thetransistor/OpenWest2015/AddOnKit/Software/BMP Loader/img/1.bmp

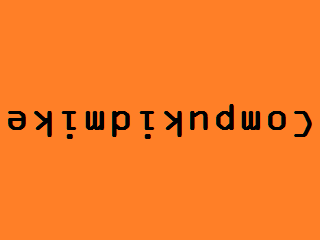
AddOnKit/Software/BMP Loader/img/1.bmp
