thetransistor/OpenWest2015/AddOnKit/Software/BMP Loader/img/default.bmp

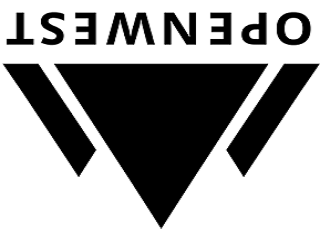
AddOnKit/Software/BMP Loader/img/default.bmp
