thetransistor/OpenWest2015/images/attiny85-board-location.jpg

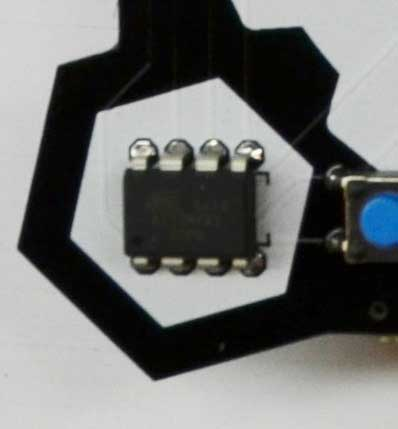
images/attiny85-board-location.jpg
