thetransistor/OpenWest2015/images/attiny85-zoom.jpg

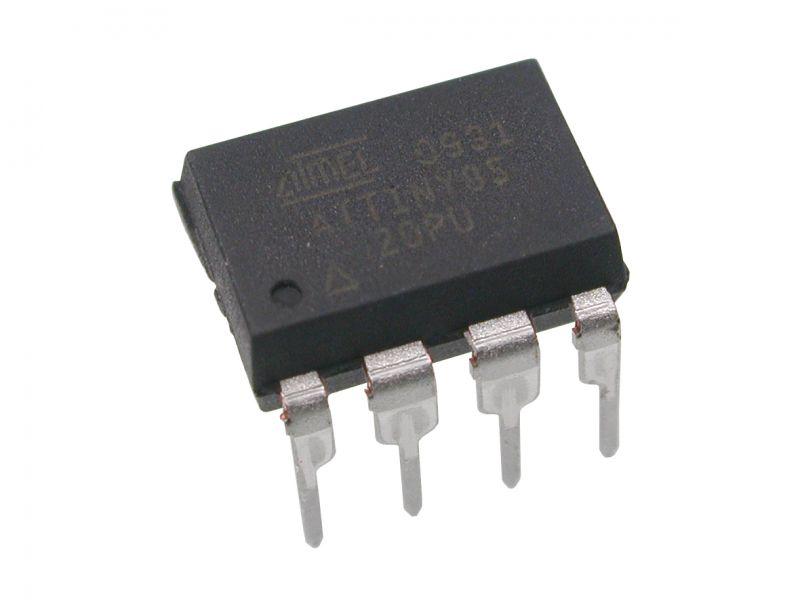
images/attiny85-zoom.jpg
