thetransistor/OpenWest2015/images/battery-holder.jpg

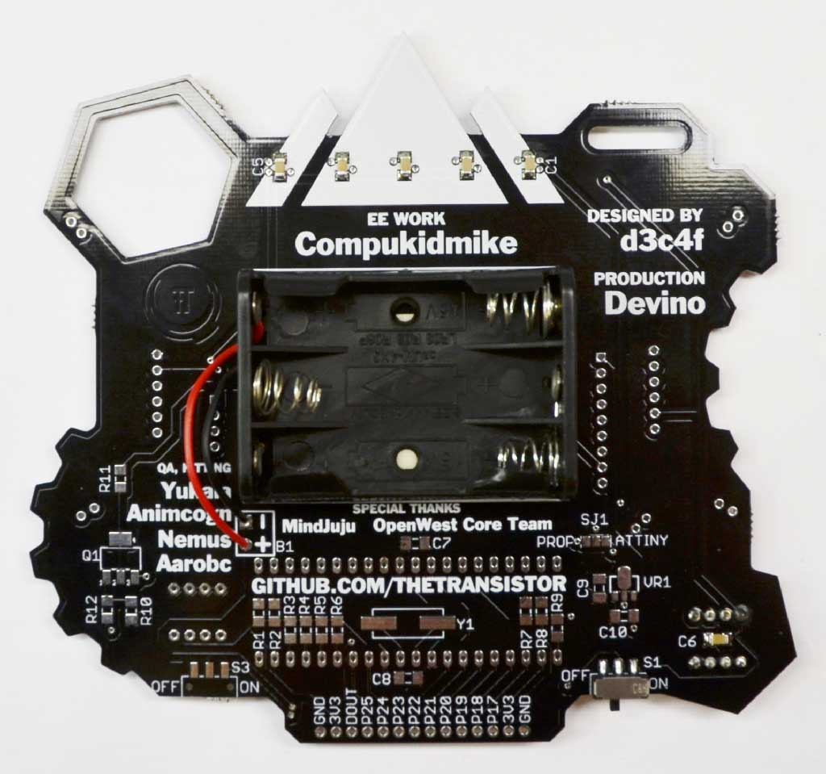
images/battery-holder.jpg
