thetransistor/OpenWest2015/images/capacitor-and-switch.jpg

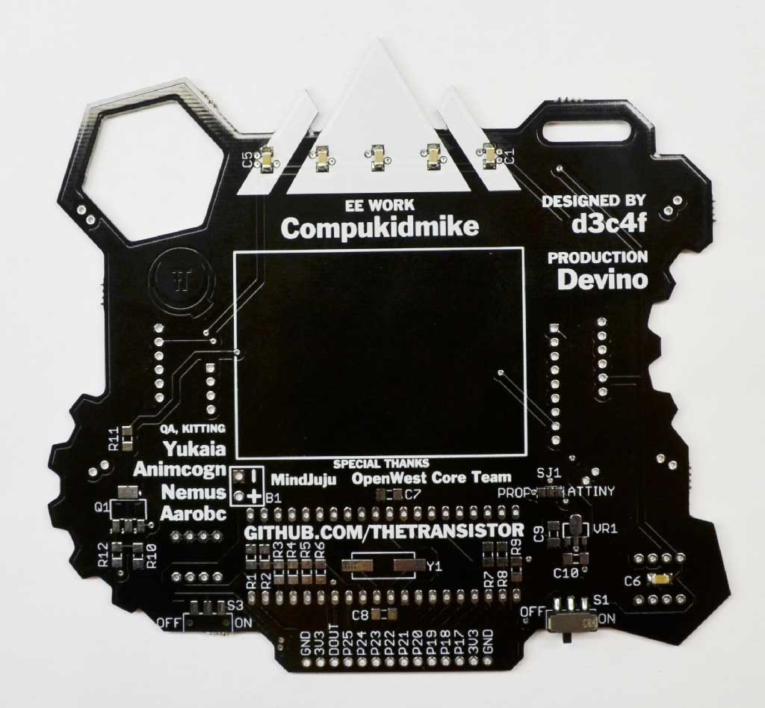
images/capacitor-and-switch.jpg
