thetransistor/OpenWest2015/images/completed-kit.jpg

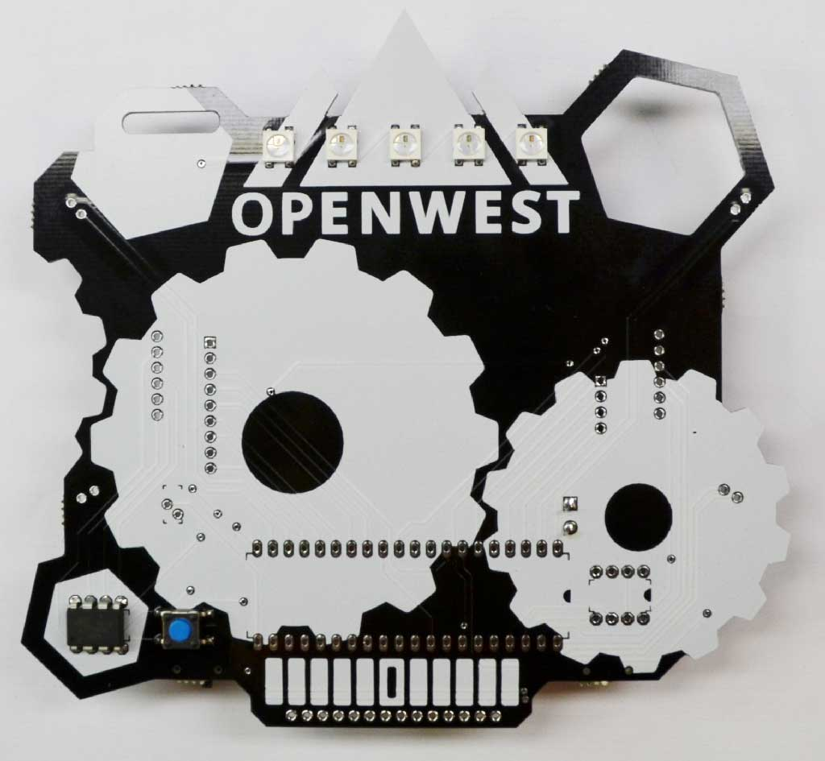
images/completed-kit.jpg
