thetransistor/OpenWest2015/images/concept-art.png

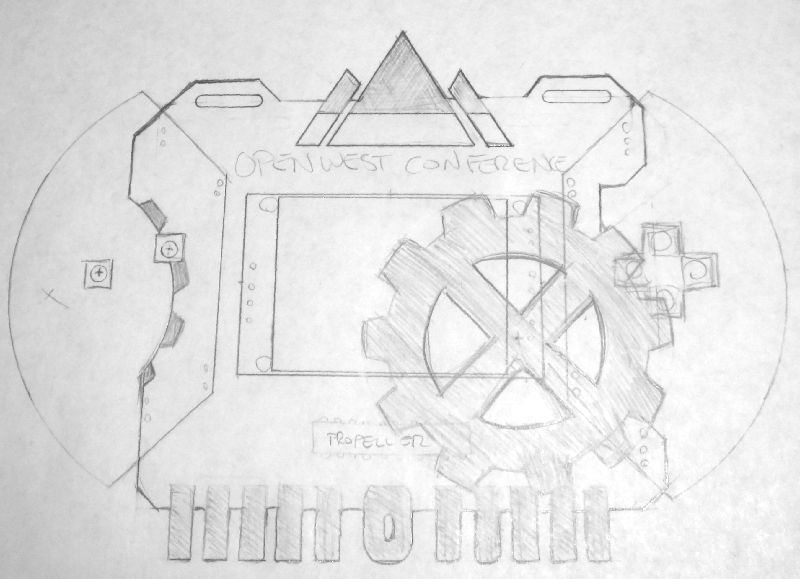
images/concept-art.png
