thetransistor/OpenWest2015/images/kit-contents.jpg

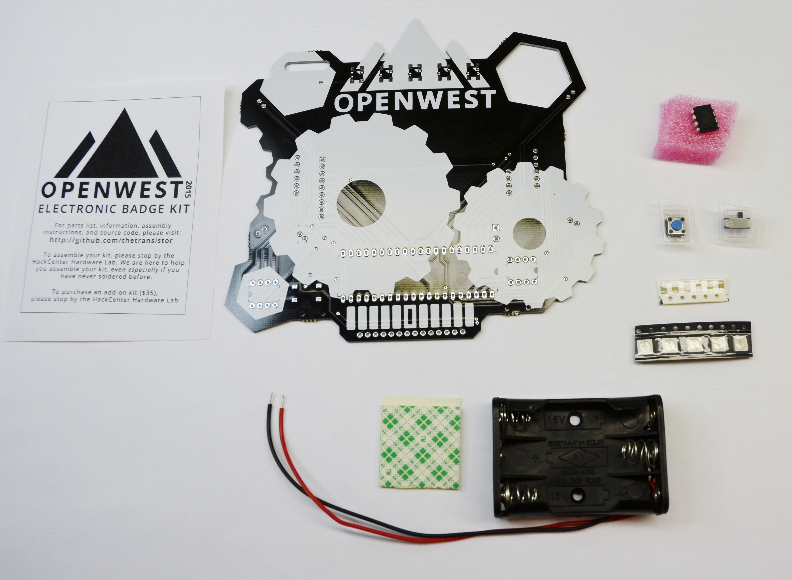
images/kit-contents.jpg
