thetransistor/OpenWest2015/images/leds-and-button.jpg

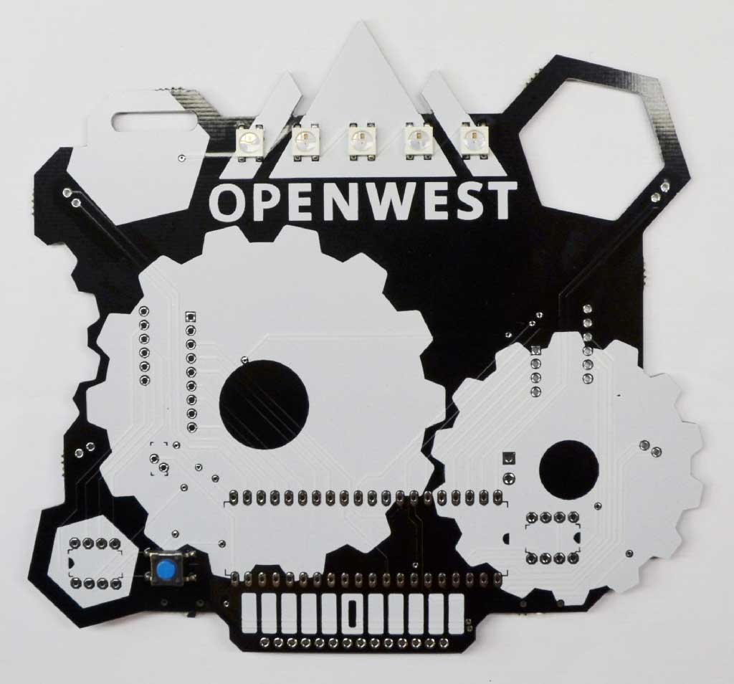
images/leds-and-button.jpg
